pingyun001/SmartCupReminder-V2/DOC/UI_Design/pic_resource/lime_img_idle.png

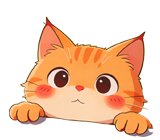
DOC/UI_Design/pic_resource/lime_img_idle.png
