pingyun001/SmartCupReminder-V2/DOC/UI_Design/pic_resource/lime_img_timeout.png

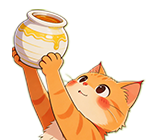
DOC/UI_Design/pic_resource/lime_img_timeout.png
