pingyun001/SmartCupReminder-V2/DOC/UI_Design/pic_resource/lime_mainbg.png

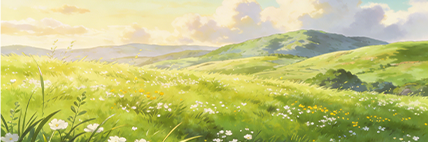
DOC/UI_Design/pic_resource/lime_mainbg.png
