pingyun001/SmartCupReminder-V2/DOC/UI_Design/pic_resource/lime_mainbg_full.png

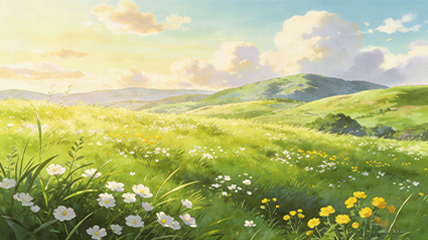
DOC/UI_Design/pic_resource/lime_mainbg_full.png
