pingyun001/SmartCupReminder-V2/SOFTWARE/LVGL_SIMULATION/Lime_Resources/LimeLvResources/dog.gif

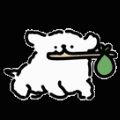
SOFTWARE/LVGL_SIMULATION/Lime_Resources/LimeLvResources/dog.gif
