pingyun001/SmartCupReminder-V2/SOFTWARE/LVGL_SIMULATION/Lime_Resources/LimeLvResources/scenery1.gif

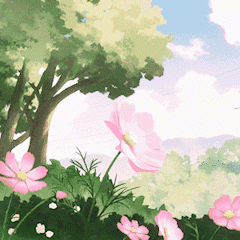
SOFTWARE/LVGL_SIMULATION/Lime_Resources/LimeLvResources/scenery1.gif
