pingyun001/SmartCupReminder-V2/SOFTWARE/LVGL_SIMULATION/Lime_Resources/LimeLvResources/Shenhe.jpg

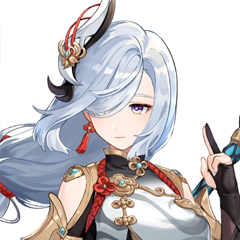
SOFTWARE/LVGL_SIMULATION/Lime_Resources/LimeLvResources/Shenhe.jpg
