pingyun001/SmartCupReminder-V2/SOFTWARE/LVGL_SIMULATION/Lime_Resources/LimeLvResources/Yunjin.jpg

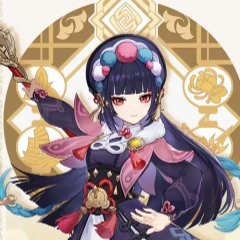
SOFTWARE/LVGL_SIMULATION/Lime_Resources/LimeLvResources/Yunjin.jpg
