pingyun001/SmartCupReminder-V2/SOFTWARE/F405_CUP_MAT_V2/Core/Src/main.c

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
/* Includes ------------------------------------------------------------------*/
#include "main.h"
#include "cmsis_os.h"
#include "adc.h"
#include "dac.h"
#include "dma.h"
#include "rtc.h"
#include "spi.h"
#include "tim.h"
#include "usart.h"
#include "usb_device.h"
#include "gpio.h"

/* USER CODE BEGIN Includes */
#include "spi_flash.h"
#include "ws2812.h"

#include "FatFsSelfTest.h"
#include "stm_system_io.h"

#include "lvgl.h"
/* USER CODE END Includes */


void SystemClock_Config(void);
void MX_FREERTOS_Init(void);
/* USER CODE BEGIN 0 */
typedef struct
{
	char head[12];
	uint32_t version;
	uint32_t app_len;
	uint32_t app_crc;
	uint32_t tag_crc;
	char end[4];
}lime_boot_tag_t;
const lime_boot_tag_t tag __attribute__(( section(".ARM.__at_0x08010400"))) = 
{
	.head = "LIME-TAG-ST",
	.version = 0xffffffff,
	.app_len = 0xffffffff,
	.app_crc = 0xffffffff,
	.tag_crc = 0xffffffff,
	.end = "END",
};
/* USER CODE END 0 */

/**
  * @brief  The application entry point.
  * @retval int
  */
int main(void)
{

  /* USER CODE BEGIN 1 */
//  SystemCoreClockUpdate();
  /* USER CODE END 1 */

  /* MCU Configuration--------------------------------------------------------*/

  /* Reset of all peripherals, Initializes the Flash interface and the Systick. */
  HAL_Init();

  /* Configure the system clock */
  SystemClock_Config();

  /* Initialize all configured peripherals */
  MX_GPIO_Init();
  MX_DMA_Init();
  MX_ADC1_Init();
  MX_DAC_Init();
  MX_TIM8_Init();
  MX_USART1_UART_Init();
  MX_USART2_UART_Init();
  MX_SPI1_Init();
  MX_SPI2_Init();
  MX_TIM4_Init();
  MX_ADC2_Init();
  MX_TIM7_Init();
  MX_TIM14_Init();
  MX_RTC_Init();
  /* USER CODE BEGIN 2 */
  DEBUG_LOG("CUP_MAT_%s Start!\n", SOFTWARE_VERSION);
  DEBUG_LOG("Compile Time:%s,%s\n", __DATE__, __TIME__);
  
  __enable_irq();

  /* USER CODE END 2 */

  /* Call init function for freertos objects (in cmsis_os2.c) */
  MX_FREERTOS_Init();

  /* Start scheduler */
  osKernelStart();

  /* We should never get here as control is now taken by the scheduler */

  /* Infinite loop */
  /* USER CODE BEGIN WHILE */
  while (1)
  {
    /* USER CODE END WHILE */

    /* USER CODE BEGIN 3 */
  }
  /* USER CODE END 3 */
}

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
/* USER CODE BEGIN 4 */

void vApplicationStackOverflowHook(xTaskHandle xTask, signed char *pcTaskName)
{
	printf("\n%s('%s')\n", __FUNCTION__, pcTaskName);
	
	while(1)
		;
}
void vApplicationMallocFailedHook(void)
{
	printf("\n%s()\n", __FUNCTION__);
	
	while(1)
		;
}

/* USER CODE END 4 */

/**
  * @brief  Period elapsed callback in non blocking mode
  * @note   This function is called  when TIM13 interrupt took place, inside
  * HAL_TIM_IRQHandler(). It makes a direct call to HAL_IncTick() to increment
  * a global variable "uwTick" used as application time base.
  * @param  htim : TIM handle
  * @retval None
  */
void HAL_TIM_PeriodElapsedCallback(TIM_HandleTypeDef *htim)
{
  if (htim->Instance == TIM13) {
    HAL_IncTick();
  }
  /* USER CODE BEGIN Callback 1 */
  if (htim->Instance == TIM13) {
	lv_tick_inc(1);
	WS2812_Sync();
  }
	
  /* USER CODE END Callback 1 */
}

/**
  * @brief  This function is executed in case of error occurrence.
  * @retval None
  */
void Error_Handler(void)
{
  /* USER CODE BEGIN Error_Handler_Debug */
	DEBUG_LOG("\n%s()\n", __FUNCTION__);
  /* User can add his own implementation to report the HAL error return state */
  __disable_irq();
  while (1)
  {
  }
  /* USER CODE END Error_Handler_Debug */
}

#ifdef  USE_FULL_ASSERT
/**
  * @brief  Reports the name of the source file and the source line number
  *         where the assert_param error has occurred.
  * @param  file: pointer to the source file name
  * @param  line: assert_param error line source number
  * @retval None
  */
void assert_failed(uint8_t *file, uint32_t line)
{
  /* USER CODE BEGIN 6 */
  /* User can add his own implementation to report the file name and line number,
     ex: printf("Wrong parameters value: file %s on line %d\r\n", file, line) */
  /* USER CODE END 6 */
}
#endif /* USE_FULL_ASSERT */
