pingyun001/SmartCupReminder-V2/SOFTWARE/F405_CUP_MAT_V2/App/lvgl_main.c

#include "lvgl_main.h"
#include "cmsis_os.h"

#include "lvgl.h"
#include "lv_demos.h"
#include "lv_port_disp.h"
#include "lcd_init.h"
#include "Lime_LvMainFace.h"

void lvgl_main(void const * argument)
{
	DEBUG_LOG("Task %s,start\n", __FUNCTION__);
	
	/* init screen */
	LCD_Init();
	
	/* Init lvgl */
	lv_init();
	lv_port_disp_init();
	
	/* create main face */
	Lime_LvMainFace_Init();
	
	while(1)
	{
		/* lvgl run handle */
		lv_timer_handler();
		
		osDelay(5);
	}
}
