pingyun001/SmartCupReminder-V2/SOFTWARE/F405_BOOTLOADER/AppLogic/exfuns.c

#include "exfuns.h"
#include <string.h>
#include "main.h"
#include "ff.h"

 #define MAX_PATHNAME_DEPTH 512 + 1  /* 最大目标文件路径+文件名深度 */

#define FILE_MAX_TYPE_NUM       7       /* 最多FILE_MAX_TYPE_NUM个大类 */
#define FILE_MAX_SUBT_NUM       4       /* 最多FILE_MAX_SUBT_NUM个小类 */

#define DYNAMIC_MEM_MELLOC		0
#if DYNAMIC_MEM_MELLOC
#include "cmsis_os.h"
#define EXFUNS_MELLOC(size)		pvPortMalloc(size)
#define EXFUNS_FREE(pin)		vPortFree(pin)
#endif

/* 文件类型列表 */
char *const FILE_TYPE_TBL[FILE_MAX_TYPE_NUM][FILE_MAX_SUBT_NUM] =
{
    {"BIN"},            /* BIN文件 */
    {"LRC"},            /* LRC文件 */
    {"NES", "SMS"},     /* NES/SMS文件 */
    {"TXT", "C", "H"},  /* 文本文件 */
    {"WAV", "MP3", "APE", "FLAC"},  /* 支持的音乐文件 */
    {"BMP", "JPG", "JPEG", "GIF"},  /* 图片文件 */
    {"AVI"},            /* 视频文件 */
};

/**
 * @brief       将小写字母转为大写字母,如果是数字,则保持不变.
 * @param       c : 要转换的字母
 * @retval      转换后的字母,大写
 */
uint8_t exfuns_char_upper(uint8_t c)
{
    if (c < 'A')return c;   /* 数字,保持不变. */

    if (c >= 'a')
    {
        return c - 0x20;    /* 变为大写. */
    }
    else
    {
        return c;           /* 大写,保持不变 */
    }
}

/**
 * @brief       报告文件的类型
 * @param       fname : 文件名
 * @retval      文件类型
 *   @arg       0XFF , 表示无法识别的文件类型编号.
 *   @arg       其他 , 高四位表示所属大类,低四位表示所属小类.
 */
uint8_t exfuns_file_type(char *fname)
{
    uint8_t tbuf[5];
    char *attr = 0;   /* 后缀名 */
    uint8_t i = 0, j;

    while (i < 250)
    {
        i++;

        if (*fname == '\0')break;   /* 偏移到了最后了. */

        fname++;
    }

    if (i == 250)return 0XFF;   /* 错误的字符串. */

    for (i = 0; i < 5; i++)     /* 得到后缀名 */
    {
        fname--;

        if (*fname == '.')
        {
            fname++;
            attr = fname;
            break;
        }
    }

    if (attr == 0)return 0XFF;

    strcpy((char *)tbuf, (const char *)attr);       /* copy */

    for (i = 0; i < 4; i++)tbuf[i] = exfuns_char_upper(tbuf[i]);    /* 全部变为大写 */

    for (i = 0; i < FILE_MAX_TYPE_NUM; i++)         /* 大类对比 */
    {
        for (j = 0; j < FILE_MAX_SUBT_NUM; j++)     /* 子类对比 */
        {
            if (*FILE_TYPE_TBL[i][j] == 0)break;    /* 此组已经没有可对比的成员了. */

            if (strcmp((const char *)FILE_TYPE_TBL[i][j], (const char *)tbuf) == 0) /* 找到了 */
            {
                return (i << 4) | j;
            }
        }
    }

    return 0XFF;    /* 没找到 */
}

/**
 * @brief       获取磁盘剩余容量
 * @param       pdrv : 磁盘编号("0:"~"9:")
 * @param       total: 总容量 (KB)
 * @param       free : 剩余容量 (KB)
 * @retval      0, 正常; 其他, 错误代码
 */
uint8_t exfuns_get_free(char *pdrv, uint32_t *total, uint32_t *free)
{
    FATFS *fs1;
    uint8_t res;
    uint32_t fre_clust = 0, fre_sect = 0, tot_sect = 0;
    
    /* 得到磁盘信息及空闲簇数量 */
    res = (uint32_t)f_getfree((const TCHAR *)pdrv, (DWORD *)&fre_clust, &fs1);

    if (res == 0)
    {
        tot_sect = (fs1->n_fatent - 2) * fs1->csize;    /* 得到总扇区数 */
        fre_sect = fre_clust * fs1->csize;              /* 得到空闲扇区数 */
#if FF_MAX_SS!=512  /* 扇区大小不是512字节,则转换为512字节 */
        tot_sect *= fs1->ssize / 512;
        fre_sect *= fs1->ssize / 512;
#endif
        *total = tot_sect >> 1;     /* 单位为KB */
        *free = fre_sect >> 1;      /* 单位为KB */
    }

    return res;
}

/**
 * @brief       文件复制
 *   @note      将psrc文件,copy到pdst.
 *              注意: 文件大小不要超过4GB.
 *
 * @param       fcpymsg : 函数指针, 用于实现拷贝时的信息显示
 *                  pname:文件/文件夹名
 *                  pct:百分比
 *                  mode:
 *                      bit0 : 更新文件名
 *                      bit1 : 更新百分比pct
 *                      bit2 : 更新文件夹
 *                      其他 : 保留
 *                  返回值: 0, 正常; 1, 强制退出;
 *
 * @param       psrc    : 源文件
 * @param       pdst    : 目标文件
 * @param       totsize : 总大小(当totsize为0的时候,表示仅仅为单个文件拷贝)
 * @param       cpdsize : 已复制了的大小.
 * @param       fwmode  : 文件写入模式
 *   @arg       0: 不覆盖原有的文件
 *   @arg       1: 覆盖原有的文件
 *
 * @retval      执行结果
 *   @arg       0   , 正常
 *   @arg       0XFF, 强制退出
 *   @arg       其他, 错误代码
 */

 
uint8_t exfuns_file_copy(uint8_t(*fcpymsg)(uint8_t *pname, uint8_t pct, uint8_t mode), uint8_t *psrc, uint8_t *pdst, 
                                      uint32_t totsize, uint32_t cpdsize, uint8_t fwmode)
{
	#define FILE_CAT_SIZE 256
	
    uint8_t res;
    uint16_t br = 0;
    uint16_t bw = 0;
    FIL *fsrc = 0;
    FIL *fdst = 0;
    uint8_t *fbuf = 0;
    uint8_t curpct = 0;
    unsigned long long lcpdsize = cpdsize;

#if DYNAMIC_MEM_MELLOC
    fsrc = (FIL *)EXFUNS_MELLOC(sizeof(FIL));    /* 申请内存 */
    fdst = (FIL *)EXFUNS_MELLOC(sizeof(FIL));
    fbuf = (uint8_t *)EXFUNS_MELLOC(FILE_CAT_SIZE);
#else
	FIL ffsrc = {0};
	FIL ffdst = {0};
	uint8_t cpyBuf[FILE_CAT_SIZE] = {0};
	fsrc = &ffsrc;
	fdst = &ffdst;
	fbuf = cpyBuf;
#endif

    if (fsrc == NULL || fdst == NULL || fbuf == NULL)
    {
        res = 100;  /* 前面的值留给fatfs */
    }
    else
    {
        if (fwmode == 0)
        {
            fwmode = FA_CREATE_NEW;     /* 不覆盖 */
        }
        else 
        {
            fwmode = FA_CREATE_ALWAYS;  /* 覆盖存在的文件 */
        }
        
        res = f_open(fsrc, (const TCHAR *)psrc, FA_READ | FA_OPEN_EXISTING);        /* 打开只读文件 */

        if (res == 0)res = f_open(fdst, (const TCHAR *)pdst, FA_WRITE | fwmode);    /* 第一个打开成功,才开始打开第二个 */

        if (res == 0)           /* 两个都打开成功了 */
        {
            if (totsize == 0)   /* 仅仅是单个文件复制 */
            {
                totsize = fsrc->obj.objsize;
                lcpdsize = 0;
                curpct = 0;
            }
            else
            {
                curpct = (lcpdsize * 100) / totsize;            /* 得到新百分比 */
            }
            
            fcpymsg(psrc, curpct, 0X02);                        /* 更新百分比 */

            while (res == 0)    /* 开始复制 */
            {
                res = f_read(fsrc, fbuf, FILE_CAT_SIZE, (UINT *)&br);    /* 源头读出512字节 */

                if (res || br == 0)break;

                res = f_write(fdst, fbuf, (UINT)br, (UINT *)&bw);/* 写入目的文件 */
                lcpdsize += bw;

                if (curpct != (lcpdsize * 100) / totsize)       /* 是否需要更新百分比 */
                {
                    curpct = (lcpdsize * 100) / totsize;

                    if (fcpymsg(psrc, curpct, 0X02))            /* 更新百分比 */
                    {
                        res = 0XFF;                             /* 强制退出 */
                        break;
                    }
                }

                if (res || bw < br)break;
            }

            f_close(fsrc);
            f_close(fdst);
        }
    }
	
#if DYNAMIC_MEM_MELLOC
    EXFUNS_FREE(fsrc); /* 释放内存 */
    EXFUNS_FREE(fdst);
    EXFUNS_FREE(fbuf);
#endif
	
    return res;
}

/**
 * @brief       得到路径下的文件夹
 *   @note      即把路径全部去掉, 只留下文件夹名字.
 * @param       pname : 详细路径 
 * @retval      0   , 路径就是个卷标号.
 *              其他, 文件夹名字首地址
 */
uint8_t *exfuns_get_src_dname(uint8_t *pname)
{
    uint16_t temp = 0;

    while (*pname != 0)
    {
        pname++;
        temp++;
    }

    if (temp < 4)return 0;

    while ((*pname != 0x5c) && (*pname != 0x2f))pname--;    /* 追述到倒数第一个"\"或者"/"处 */

    return ++pname;
}

/**
 * @brief       得到文件夹大小
 *   @note      注意: 文件夹大小不要超过4GB.
 * @param       pname : 详细路径 
 * @retval      0   , 文件夹大小为0, 或者读取过程中发生了错误.
 *              其他, 文件夹大小
 */
#if !DYNAMIC_MEM_MELLOC
static uint8_t folderSizeBufScr[MAX_PATHNAME_DEPTH] = {0};
#endif
uint32_t exfuns_get_folder_size(uint8_t *fdname)
{
    uint8_t res = 0;
    DIR *fddir = 0;         /* 目录 */
    FILINFO *finfo = 0;     /* 文件信息 */
    uint8_t *pathname = 0;  /* 目标文件夹路径+文件名 */
    uint16_t pathlen = 0;   /* 目标路径长度 */
    uint32_t fdsize = 0;

#if DYNAMIC_MEM_MELLOC
    fddir = (DIR *)EXFUNS_MELLOC(sizeof(DIR));   /* 申请内存 */
    finfo = (FILINFO *)EXFUNS_MELLOC(sizeof(FILINFO));
#else
	DIR ffddir = {0};
	FILINFO ffinfo = {0};
	fddir = &ffddir;
	finfo = &ffinfo;
#endif
    if (fddir == NULL || finfo == NULL)res = 100;

    if (res == 0)
    {
#if DYNAMIC_MEM_MELLOC
        pathname = EXFUNS_MELLOC(MAX_PATHNAME_DEPTH);
#else
		memset(folderSizeBufScr, 0, sizeof(folderSizeBufScr));
		pathname = folderSizeBufScr;
#endif
        if (pathname == NULL)res = 101;

        if (res == 0)
        {
            pathname[0] = 0;
            strcat((char *)pathname, (const char *)fdname);     /* 复制路径 */
            res = f_opendir(fddir, (const TCHAR *)fdname);      /* 打开源目录 */

            if (res == 0)   /* 打开目录成功 */
            {
                while (res == 0)   /* 开始复制文件夹里面的东东 */
                {
                    res = f_readdir(fddir, finfo);                  /* 读取目录下的一个文件 */

                    if (res != FR_OK || finfo->fname[0] == 0)break; /* 错误了/到末尾了,退出 */

                    if (finfo->fname[0] == '.')continue;            /* 忽略上级目录 */

                    if (finfo->fattrib & 0X10)   /* 是子目录(文件属性,0X20,归档文件;0X10,子目录;) */
                    {
                        pathlen = strlen((const char *)pathname);   /* 得到当前路径的长度 */
                        strcat((char *)pathname, (const char *)"/");/* 加斜杠 */
                        strcat((char *)pathname, (const char *)finfo->fname);   /* 源路径加上子目录名字 */
                        //printf("\r\nsub folder:%s\r\n",pathname);      /* 打印子目录名 */
                        fdsize += exfuns_get_folder_size(pathname);     /* 得到子目录大小,递归调用 */
                        pathname[pathlen] = 0;                          /* 加入结束符 */
                    }
                    else
                    {
                        fdsize += finfo->fsize; /* 非目录,直接加上文件的大小 */
                    }
                }
            }
#if DYNAMIC_MEM_MELLOC
            EXFUNS_FREE(pathname);
#endif
        }
    }
#if DYNAMIC_MEM_MELLOC
    EXFUNS_FREE(fddir);
    EXFUNS_FREE(finfo);
#endif

    if (res)
    {
        return 0;
    }
    else 
    {
        return fdsize;
    }
}

/**
 * @brief       文件夹复制
 *   @note      将psrc文件夹, 拷贝到pdst文件夹.
 *              注意: 文件大小不要超过4GB.
 *
 * @param       fcpymsg : 函数指针, 用于实现拷贝时的信息显示
 *                  pname:文件/文件夹名
 *                  pct:百分比
 *                  mode:
 *                      bit0 : 更新文件名
 *                      bit1 : 更新百分比pct
 *                      bit2 : 更新文件夹
 *                      其他 : 保留
 *                  返回值: 0, 正常; 1, 强制退出;
 *
 * @param       psrc    : 源文件夹
 * @param       pdst    : 目标文件夹
 *   @note      必须形如"X:"/"X:XX"/"X:XX/XX"之类的. 且要确认上一级文件夹存在
 *
 * @param       totsize : 总大小(当totsize为0的时候,表示仅仅为单个文件拷贝)
 * @param       cpdsize : 已复制了的大小.
 * @param       fwmode  : 文件写入模式
 *   @arg       0: 不覆盖原有的文件
 *   @arg       1: 覆盖原有的文件
 *
 * @retval      执行结果
 *   @arg       0   , 正常
 *   @arg       0XFF, 强制退出
 *   @arg       其他, 错误代码
 */

#if !DYNAMIC_MEM_MELLOC
static uint8_t folderNameBufScr[MAX_PATHNAME_DEPTH] = {0};
static uint8_t folderNameBufDst[MAX_PATHNAME_DEPTH] = {0};
#endif
uint8_t exfuns_folder_copy(uint8_t(*fcpymsg)(uint8_t *pname, uint8_t pct, uint8_t mode), uint8_t *psrc, uint8_t *pdst, 
                           uint32_t *totsize, uint32_t *cpdsize, uint8_t fwmode)
{

    uint8_t res = 0;
    DIR *srcdir = 0;    /* 源目录 */
    DIR *dstdir = 0;    /* 源目录 */
    FILINFO *finfo = 0; /* 文件信息 */
    uint8_t *fn = 0;    /* 长文件名 */

    uint8_t *dstpathname = 0;   /* 目标文件夹路径+文件名 */
    uint8_t *srcpathname = 0;   /* 源文件夹路径+文件名 */

    uint16_t dstpathlen = 0;    /* 目标路径长度 */
    uint16_t srcpathlen = 0;    /* 源路径长度 */

#if DYNAMIC_MEM_MELLOC
    srcdir = (DIR *)EXFUNS_MELLOC(sizeof(DIR));  /* 申请内存 */
    dstdir = (DIR *)EXFUNS_MELLOC(sizeof(DIR));
    finfo = (FILINFO *)EXFUNS_MELLOC(sizeof(FILINFO));
#else
	DIR ssrcdir = {0};
	DIR ddstdir = {0};
	FILINFO ffinfo = {0};
	srcdir = &ssrcdir;
	dstdir = &ddstdir;
	finfo = &ffinfo;
#endif

    if (srcdir == NULL || dstdir == NULL || finfo == NULL)res = 100;

    if (res == 0)
    {
#if DYNAMIC_MEM_MELLOC
        dstpathname = EXFUNS_MELLOC(MAX_PATHNAME_DEPTH);
        srcpathname = EXFUNS_MELLOC(MAX_PATHNAME_DEPTH);
#else
		memset(folderNameBufDst, 0, sizeof(folderNameBufDst));
		memset(folderNameBufScr, 0, sizeof(folderNameBufScr));
		dstpathname = folderNameBufDst;
		srcpathname = folderNameBufScr;
#endif
        if (dstpathname == NULL || srcpathname == NULL)res = 101;

        if (res == 0)
        {
            dstpathname[0] = 0;
            srcpathname[0] = 0;
            strcat((char *)srcpathname, (const char *)psrc);    /* 复制原始源文件路径 */
            strcat((char *)dstpathname, (const char *)pdst);    /* 复制原始目标文件路径 */
            res = f_opendir(srcdir, (const TCHAR *)psrc);       /* 打开源目录 */

            if (res == 0)   /* 打开目录成功 */
            {
                strcat((char *)dstpathname, (const char *)"/"); /* 加入斜杠 */
                fn = exfuns_get_src_dname(psrc);

                if (fn == 0)   /* 不需要卷标拷贝 */
                {
					dstpathlen = strlen((const char *)dstpathname);
					dstpathname[dstpathlen] = 0;
//                    dstpathname[dstpathlen] = psrc[0];  /* 记录卷标 */
//                    dstpathname[dstpathlen + 1] = 0;    /* 结束符 */
                }
                else strcat((char *)dstpathname, (const char *)fn); /* 加文件名 */

                fcpymsg(dstpathname, 0, 0X04);   /* 更新文件夹名 */
                res = f_mkdir((const TCHAR *)dstpathname);  /* 如果文件夹已经存在,就不创建.如果不存在就创建新的文件夹. */

                if (res == FR_EXIST)res = 0;

                while (res == 0)   /* 开始复制文件夹里面的东东 */
                {
                    res = f_readdir(srcdir, finfo);         /* 读取目录下的一个文件 */

                    if (res != FR_OK || finfo->fname[0] == 0)break; /* 错误了/到末尾了,退出 */

                    if (finfo->fname[0] == '.')continue;    /* 忽略上级目录 */

                    fn = (uint8_t *)finfo->fname;           /* 得到文件名 */
                    dstpathlen = strlen((const char *)dstpathname); /* 得到当前目标路径的长度 */
                    srcpathlen = strlen((const char *)srcpathname); /* 得到源路径长度 */

                    strcat((char *)srcpathname, (const char *)"/"); /* 源路径加斜杠 */

                    if (finfo->fattrib & 0X10)  /* 是子目录(文件属性,0X20,归档文件;0X10,子目录;) */
                    {
#if DYNAMIC_MEM_MELLOC	/* 静态不支持递归文件夹复制 */
                        strcat((char *)srcpathname, (const char *)fn);  /* 源路径加上子目录名字 */
                        res = exfuns_folder_copy(fcpymsg, srcpathname, dstpathname, totsize, cpdsize, fwmode);   /* 拷贝文件夹 */
#endif
                    }
                    else     /* 非目录 */
                    {
                        strcat((char *)dstpathname, (const char *)"/"); /* 目标路径加斜杠 */
                        strcat((char *)dstpathname, (const char *)fn);  /* 目标路径加文件名 */
                        strcat((char *)srcpathname, (const char *)fn);  /* 源路径加文件名 */
                        fcpymsg(fn, 0, 0X01);       /* 更新文件名 */
                        res = exfuns_file_copy(fcpymsg, srcpathname, dstpathname, *totsize, *cpdsize, fwmode);  /* 复制文件 */
                        *cpdsize += finfo->fsize;   /* 增加一个文件大小 */
                    }

                    srcpathname[srcpathlen] = 0;    /* 加入结束符 */
                    dstpathname[dstpathlen] = 0;    /* 加入结束符 */
                }
            }
			
#if DYNAMIC_MEM_MELLOC
            EXFUNS_FREE(dstpathname);
            EXFUNS_FREE(srcpathname);
#endif
        }
    }
	
#if DYNAMIC_MEM_MELLOC
    EXFUNS_FREE(srcdir);
    EXFUNS_FREE(dstdir);
    EXFUNS_FREE(finfo);
#endif
    return res;
}
