pingyun001/SmartCupReminder-V2/SOFTWARE/F405_BOOTLOADER/Core/Src/usart.c

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
/* Includes ------------------------------------------------------------------*/
#include "usart.h"

/* USER CODE BEGIN 0 */
#include <stdio.h>

#if defined(__ARMCC_VERSION) && (__ARMCC_VERSION > 6000000)

#define COMPILER_IS_V6	1
#else

#define COMPILER_IS_V5	1
#endif

#ifdef COMPILER_IS_V6
#if !defined(__MICROLIB)
__asm (".global __use_no_semihosting\n\t");
void _sys_exit(int x)
{
  x = x;
}
//__use_no_semihosting was requested, but _ttywrch was 
void _ttywrch(int ch)
{
    ch = ch;
}
FILE __stdout;
#endif		//!defined(__MICROLIB)

#if defined ( __GNUC__ ) && !defined (__clang__) 
#define PUTCHAR_PROTOTYPE int __io_putchar(int ch)
#else
#define PUTCHAR_PROTOTYPE int fputc(int ch, FILE *f)
#endif 
PUTCHAR_PROTOTYPE
{


	while((USART1 -> SR & 0X40) == 0){}
    USART1->DR = (uint8_t )ch;
  return ch;
}
#endif
#ifdef COMPILER_IS_V5
#pragma import(__use_no_semihosting)                             
struct __FILE { 
    int handle; 
}; 

FILE __stdout;          
void _sys_exit(int x) { 
    x = x; 
}
int fputc(int ch, FILE *f){      
    while((USART1 -> SR & 0X40) == 0){}
    USART1->DR = (uint8_t )ch;
    return ch;
}
#endif	//(COMPILER_IS_V5)

/* USER CODE END 0 */

UART_HandleTypeDef huart1;
UART_HandleTypeDef huart2;
DMA_HandleTypeDef hdma_usart2_tx;

/* USART1 init function */

void MX_USART1_UART_Init(void)
{

  huart1.Instance = USART1;
  huart1.Init.BaudRate = 115200;
  huart1.Init.WordLength = UART_WORDLENGTH_8B;
  huart1.Init.StopBits = UART_STOPBITS_1;
  huart1.Init.Parity = UART_PARITY_NONE;
  huart1.Init.Mode = UART_MODE_TX_RX;
  huart1.Init.HwFlowCtl = UART_HWCONTROL_NONE;
  huart1.Init.OverSampling = UART_OVERSAMPLING_16;
  if (HAL_UART_Init(&huart1) != HAL_OK)
  {
    Error_Handler();
  }
}
/* USART2 init function */

void MX_USART2_UART_Init(void)
{

  huart2.Instance = USART2;
  huart2.Init.BaudRate = 9600;
  huart2.Init.WordLength = UART_WORDLENGTH_8B;
  huart2.Init.StopBits = UART_STOPBITS_1;
  huart2.Init.Parity = UART_PARITY_NONE;
  huart2.Init.Mode = UART_MODE_TX_RX;
  huart2.Init.HwFlowCtl = UART_HWCONTROL_NONE;
  huart2.Init.OverSampling = UART_OVERSAMPLING_16;
  if (HAL_UART_Init(&huart2) != HAL_OK)
  {
    Error_Handler();
  }
}

void HAL_UART_MspInit(UART_HandleTypeDef* uartHandle)
{

  GPIO_InitTypeDef GPIO_InitStruct = {0};
  if(uartHandle->Instance==USART1)
  {
    /* USART1 clock enable */
    __HAL_RCC_USART1_CLK_ENABLE();

    __HAL_RCC_GPIOA_CLK_ENABLE();
    /**USART1 GPIO Configuration
    PA9     ------> USART1_TX
    PA10     ------> USART1_RX
    */
    GPIO_InitStruct.Pin = GPIO_PIN_9|GPIO_PIN_10;
    GPIO_InitStruct.Mode = GPIO_MODE_AF_PP;
    GPIO_InitStruct.Pull = GPIO_NOPULL;
    GPIO_InitStruct.Speed = GPIO_SPEED_FREQ_VERY_HIGH;
    GPIO_InitStruct.Alternate = GPIO_AF7_USART1;
    HAL_GPIO_Init(GPIOA, &GPIO_InitStruct);

  }
  else if(uartHandle->Instance==USART2)
  {
    /* USART2 clock enable */
    __HAL_RCC_USART2_CLK_ENABLE();

    __HAL_RCC_GPIOA_CLK_ENABLE();
    /**USART2 GPIO Configuration
    PA2     ------> USART2_TX
    PA3     ------> USART2_RX
    */
    GPIO_InitStruct.Pin = GPIO_PIN_2|GPIO_PIN_3;
    GPIO_InitStruct.Mode = GPIO_MODE_AF_PP;
    GPIO_InitStruct.Pull = GPIO_NOPULL;
    GPIO_InitStruct.Speed = GPIO_SPEED_FREQ_VERY_HIGH;
    GPIO_InitStruct.Alternate = GPIO_AF7_USART2;
    HAL_GPIO_Init(GPIOA, &GPIO_InitStruct);

    /* USART2 DMA Init */
    /* USART2_TX Init */
    hdma_usart2_tx.Instance = DMA1_Stream6;
    hdma_usart2_tx.Init.Channel = DMA_CHANNEL_4;
    hdma_usart2_tx.Init.Direction = DMA_MEMORY_TO_PERIPH;
    hdma_usart2_tx.Init.PeriphInc = DMA_PINC_DISABLE;
    hdma_usart2_tx.Init.MemInc = DMA_MINC_ENABLE;
    hdma_usart2_tx.Init.PeriphDataAlignment = DMA_PDATAALIGN_BYTE;
    hdma_usart2_tx.Init.MemDataAlignment = DMA_MDATAALIGN_BYTE;
    hdma_usart2_tx.Init.Mode = DMA_NORMAL;
    hdma_usart2_tx.Init.Priority = DMA_PRIORITY_LOW;
    hdma_usart2_tx.Init.FIFOMode = DMA_FIFOMODE_DISABLE;
    if (HAL_DMA_Init(&hdma_usart2_tx) != HAL_OK)
    {
      Error_Handler();
    }

    __HAL_LINKDMA(uartHandle,hdmatx,hdma_usart2_tx);

    /* USART2 interrupt Init */
    HAL_NVIC_SetPriority(USART2_IRQn, 7, 0);
    HAL_NVIC_EnableIRQ(USART2_IRQn);
  }
}

void HAL_UART_MspDeInit(UART_HandleTypeDef* uartHandle)
{

  if(uartHandle->Instance==USART1)
  {
    /* Peripheral clock disable */
    __HAL_RCC_USART1_CLK_DISABLE();

    /**USART1 GPIO Configuration
    PA9     ------> USART1_TX
    PA10     ------> USART1_RX
    */
    HAL_GPIO_DeInit(GPIOA, GPIO_PIN_9|GPIO_PIN_10);

  }
  else if(uartHandle->Instance==USART2)
  {
    /* Peripheral clock disable */
    __HAL_RCC_USART2_CLK_DISABLE();

    /**USART2 GPIO Configuration
    PA2     ------> USART2_TX
    PA3     ------> USART2_RX
    */
    HAL_GPIO_DeInit(GPIOA, GPIO_PIN_2|GPIO_PIN_3);

    /* USART2 DMA DeInit */
    HAL_DMA_DeInit(uartHandle->hdmatx);

    /* USART2 interrupt Deinit */
    HAL_NVIC_DisableIRQ(USART2_IRQn);
  }
}
