pingyun001/SmartCupReminder-V2/SOFTWARE/F405_BOOTLOADER/AppLogic/stm_system_io.h

#ifndef __STM_SYSTEM_IO_H__
#define __STM_SYSTEM_IO_H__

#include "main.h"


void lime_stm_system_restart(void);

void lime_stm_system_restore(void);

void lime_stm_system_enter_u_disk_mode(void);

void lime_stm_system_exit_u_disk_mode(void);

#endif //__STM_SYSTEM_IO_H__
